jaw0/amiketo/src/lsm303d.h

// SA0 = Gnd
#define LSM303D_ADDRESS          (0x3C >> 1)         // 0011001x
#define LSM303D_WHOAMI		    0x49

#define LSM303D_REGISTER_TEMP_OUT_L 0x05
#define LSM303D_REGISTER_TEMP_OUT_H 0x06
#define LSM303D_REGISTER_STATUS_M   0x07
#define LSM303D_REGISTER_OUT_X_L_M  0x08
#define LSM303D_REGISTER_OUT_X_H_M  0x09
#define LSM303D_REGISTER_OUT_Y_L_M  0x0A
#define LSM303D_REGISTER_OUT_Y_H_M  0x0B
#define LSM303D_REGISTER_OUT_Z_L_M  0x0C
#define LSM303D_REGISTER_OUT_Z_H_M  0x0D
#define LSM303D_REGISTER_WHOAMI	    0x0F // reads as 0x49
#define LSM303D_REGISTER_CTRL0	    0x1F
#define LSM303D_REGISTER_CTRL1	    0x20
#define LSM303D_REGISTER_CTRL2	    0x21
#define LSM303D_REGISTER_CTRL3	    0x22
#define LSM303D_REGISTER_CTRL4	    0x23
#define LSM303D_REGISTER_CTRL5	    0x24
#define LSM303D_REGISTER_CTRL6	    0x25
#define LSM303D_REGISTER_CTRL7	    0x26
#define LSM303D_REGISTER_STATUS_A   0x27
#define LSM303D_REGISTER_OUT_X_L_A  0x28
#define LSM303D_REGISTER_OUT_X_H_A  0x29
#define LSM303D_REGISTER_OUT_Y_L_A  0x2A
#define LSM303D_REGISTER_OUT_Y_H_A  0x2B
#define LSM303D_REGISTER_OUT_Z_L_A  0x2C
#define LSM303D_REGISTER_OUT_Z_H_A  0x2D
